s-gv/cookoo/pcb/pcb_bottom.png

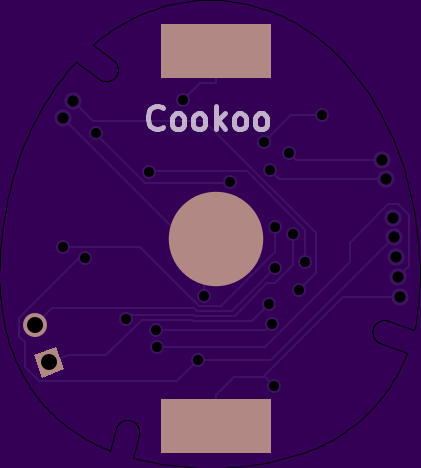
pcb/pcb_bottom.png
