s-gv/cookoo/pcb/pcb_top.png

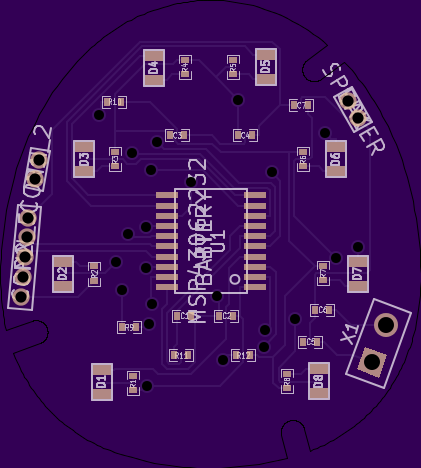
pcb/pcb_top.png
