s-gv/cookoo/pcb/pcb_assembly_assist.png

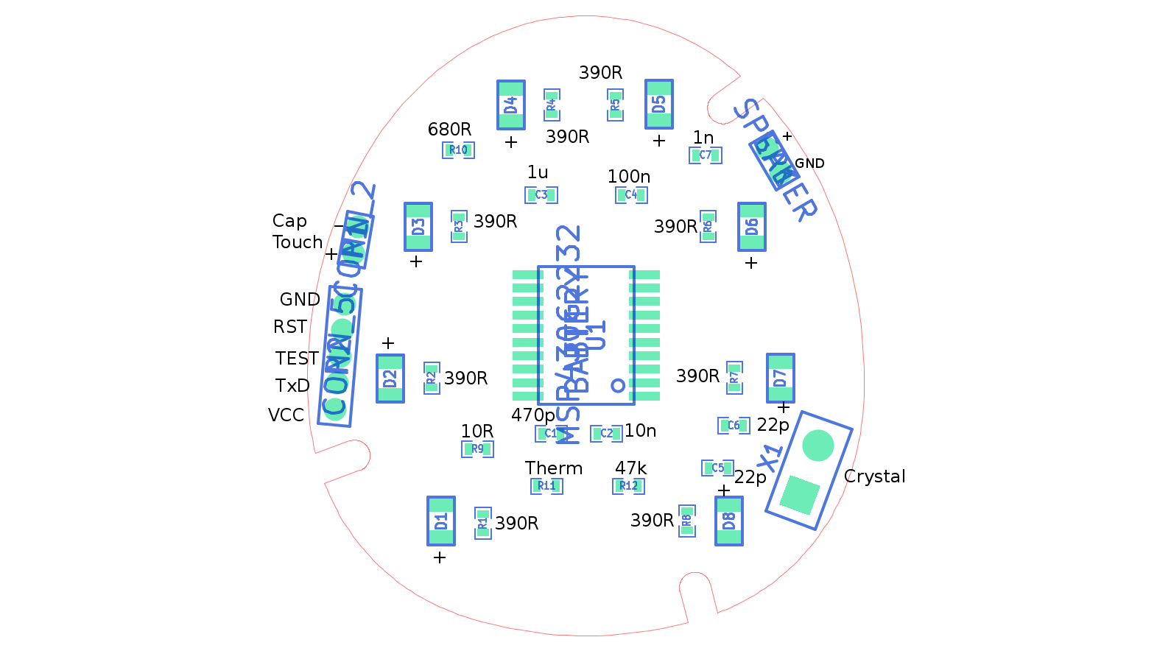
pcb/pcb_assembly_assist.png
