s-gv/cookoo/schematic/TI_launchpad_as_ISP_wiring.png

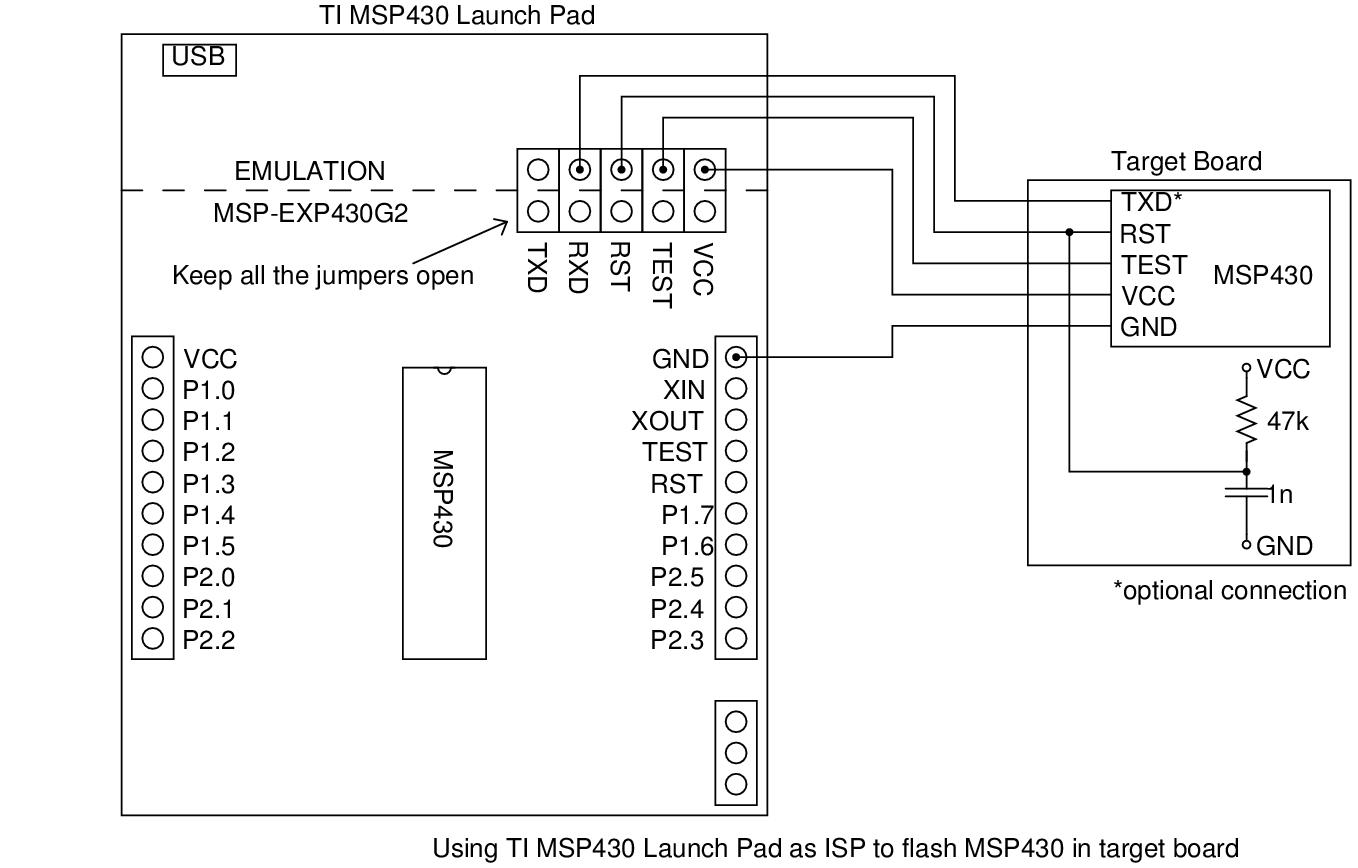
schematic/TI_launchpad_as_ISP_wiring.png
